LispEngineer/stm-midi-poc1/jlcpcb-production/run2-20241221/JCLPCB-3D-back.png

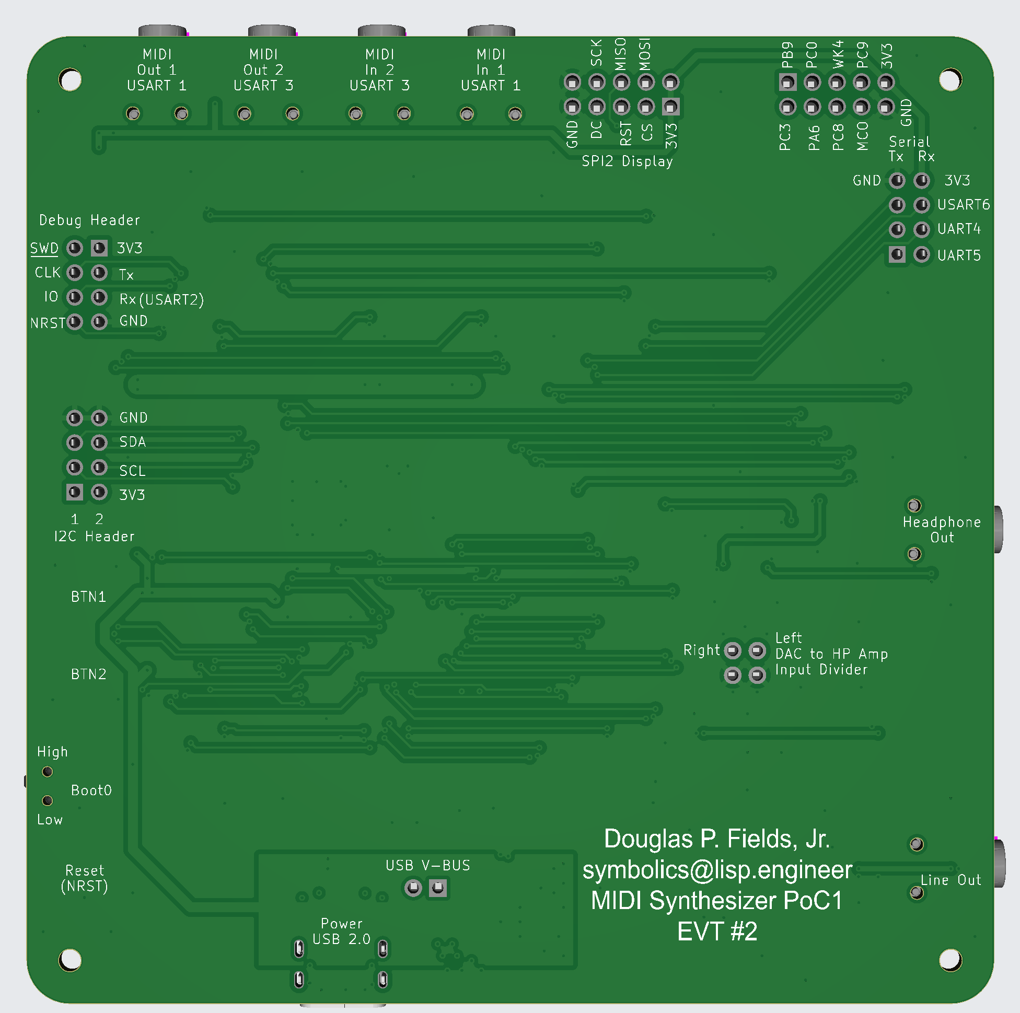
jlcpcb-production/run2-20241221/JCLPCB-3D-back.png
