LispEngineer/stm-midi-poc1/jlcpcb-production/run2-20241221/JLCPCB-3D-front.png

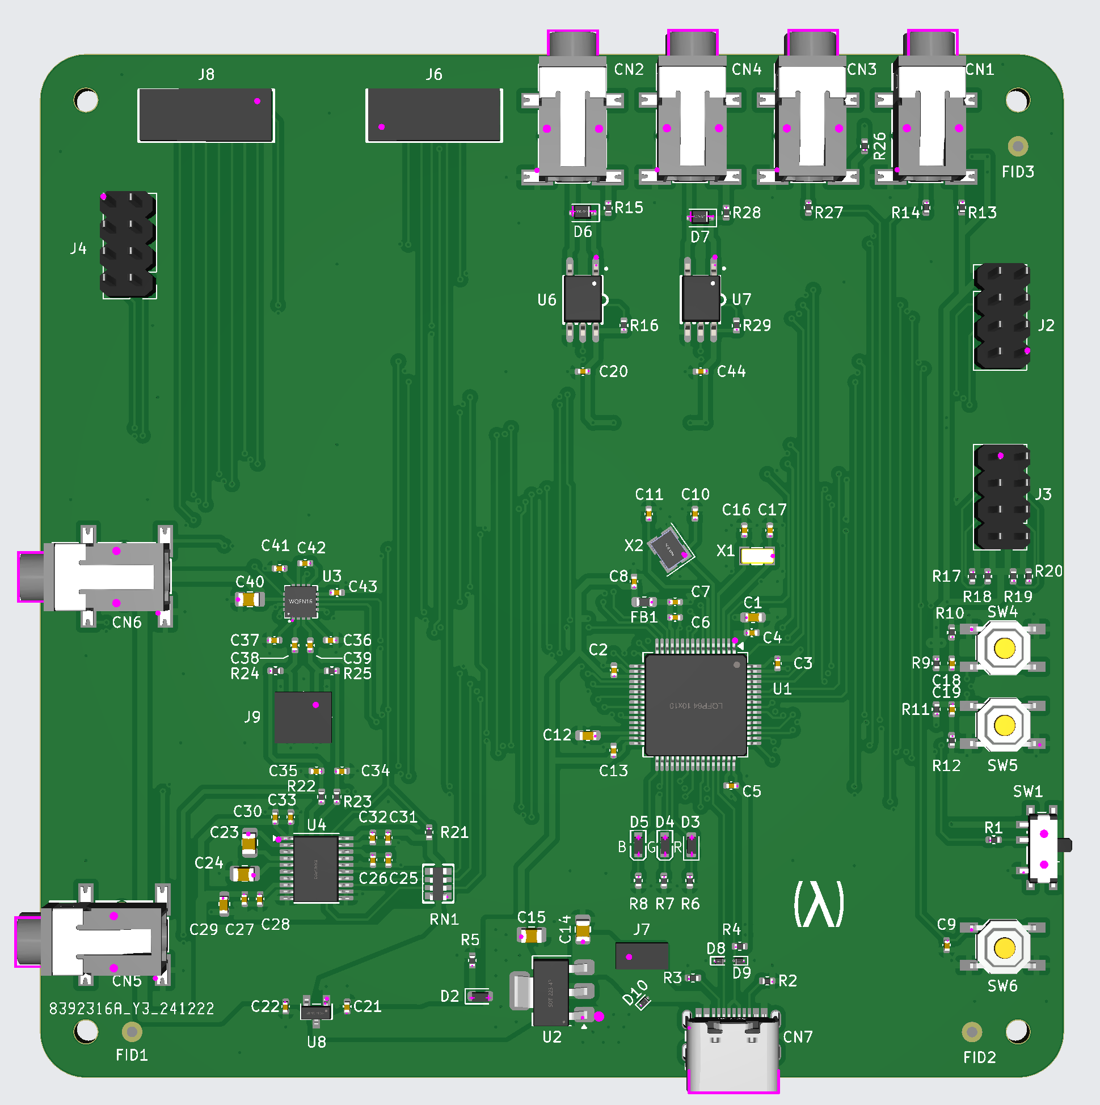
jlcpcb-production/run2-20241221/JLCPCB-3D-front.png
