LispEngineer/stm-midi-poc1/jlcpcb-production/run2-20241221/pcb-back.png

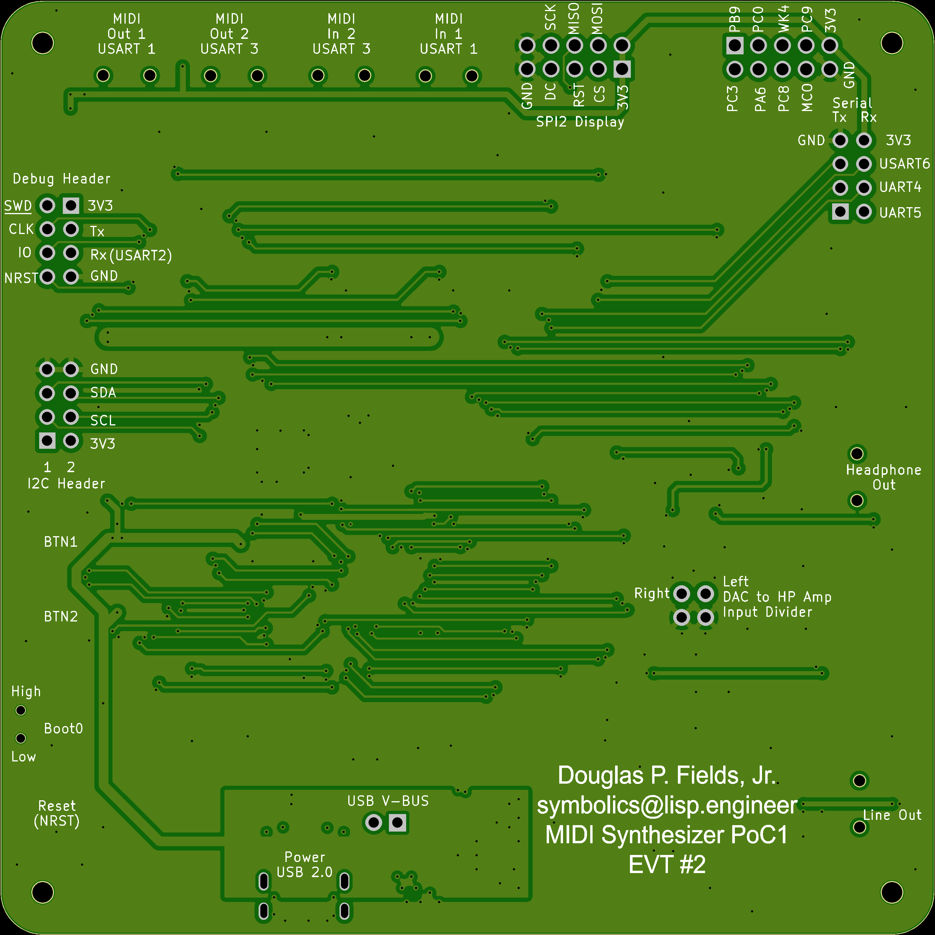
jlcpcb-production/run2-20241221/pcb-back.png
