LispEngineer/stm-midi-poc1/jlcpcb-production/run2-20241221/pcb-front.png

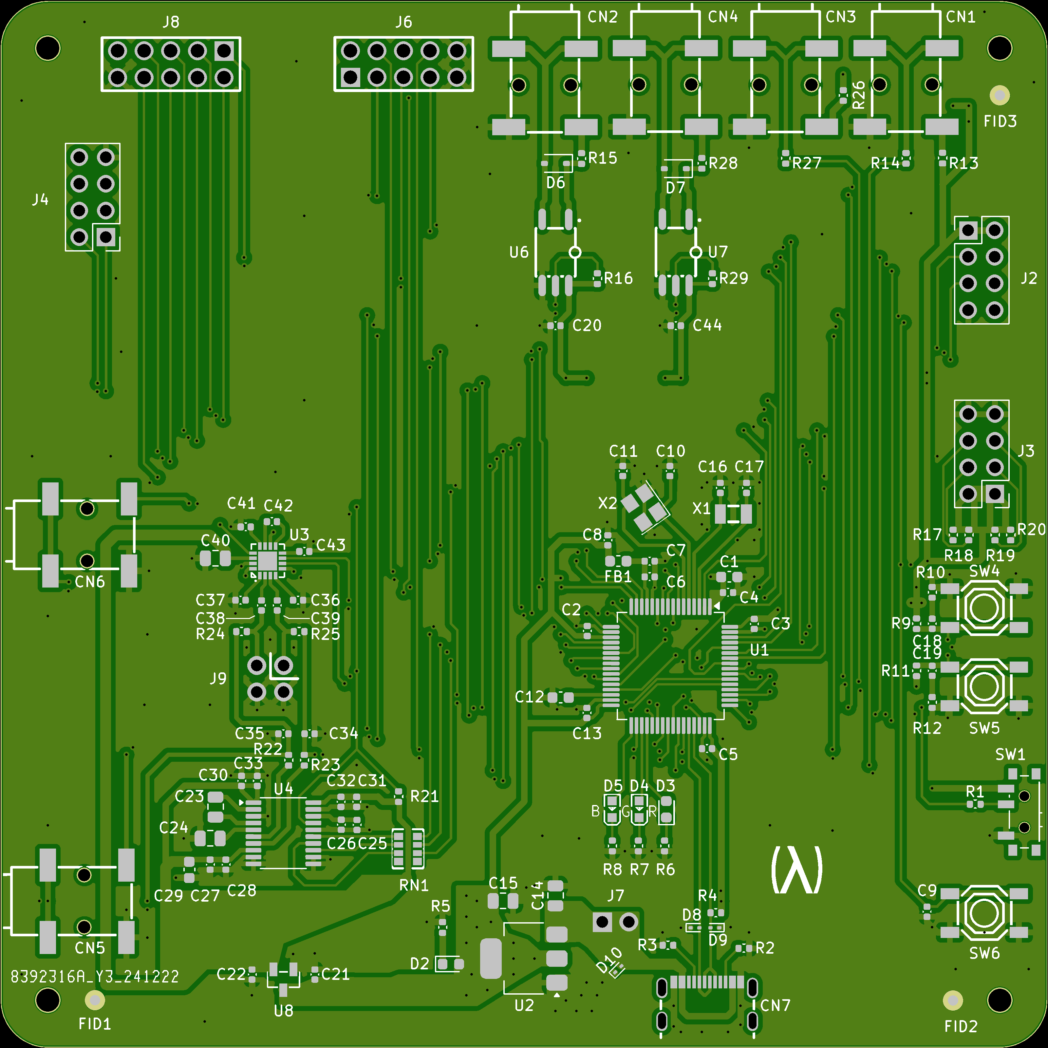
jlcpcb-production/run2-20241221/pcb-front.png
